protieusz/Fanta-Manta/STLs/SplitCase/FANTA MANTACaseRIGHT.stl

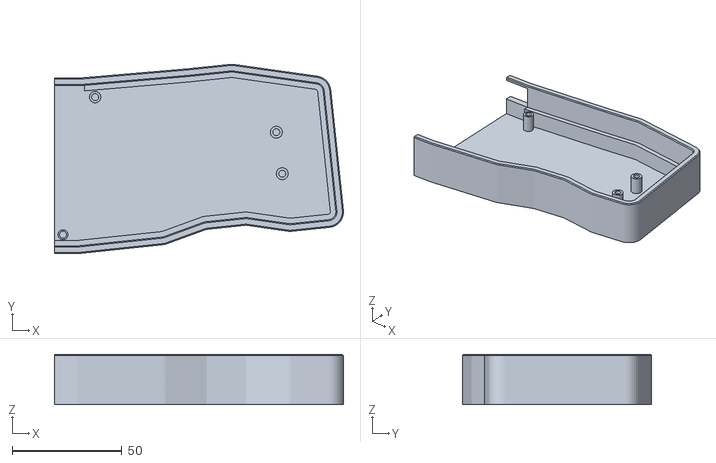
[picture p16: CAD file, 2024-04-09]
STLs/SplitCase/FANTA MANTACaseRIGHT.stl
131.4 x 86.1 x 22.8
