protieusz/Fanta-Manta/STLs/FANTA MANTARightWingLogo.stl

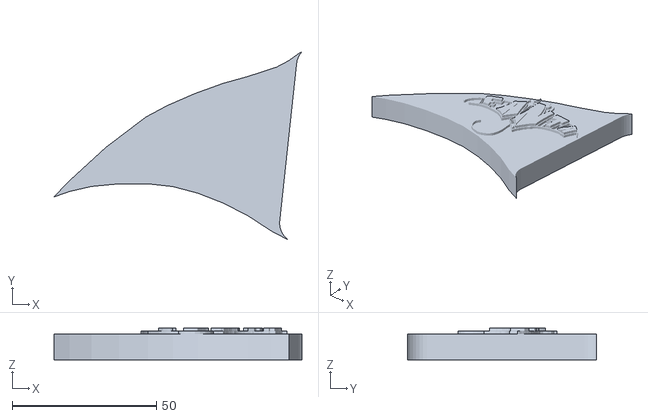
[picture p17: CAD file, 2024-04-09]
STLs/FANTA MANTARightWingLogo.stl
86.0 x 65.4 x 11.0
