protieusz/Fanta-Manta/STLs/FANTA MANTAHead.stl

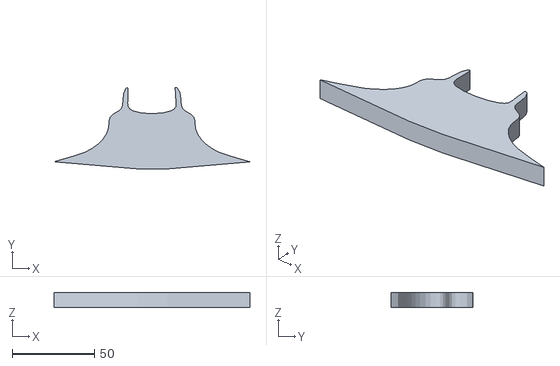
[picture p18: CAD file, 2024-04-09]
STLs/FANTA MANTAHead.stl
118.8 x 49.6 x 9.00
