protieusz/Fanta-Manta/STLs/FANTA MANTALeftWing.stl

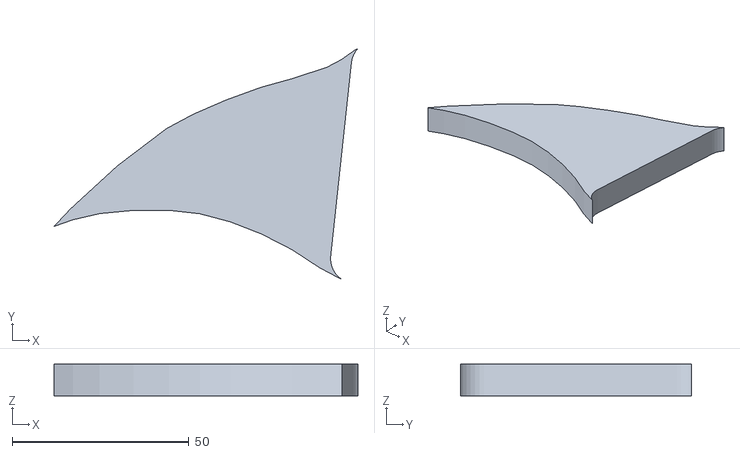
[picture p19: CAD file, 2024-04-09]
STLs/FANTA MANTALeftWing.stl
86.0 x 65.4 x 9.00
