protieusz/Fanta-Manta/STLs/FANTA MANTALeftWingLogo.stl

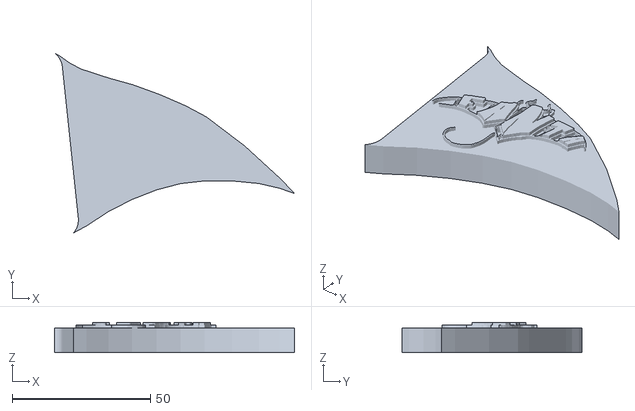
[picture p20: CAD file, 2024-04-09]
STLs/FANTA MANTALeftWingLogo.stl
86.8 x 65.1 x 11.0
